ChrisBall/PianoLuce/Arduino/Piano2Midi_Master_Reader/buttonUpdate.ino

void buttonUpdate() {
  for (int i = 0; i < 3; i++) {
    boolean buttonState = digitalRead(buttonPins[i]);
    if (buttonStates[i] == 3) {
      buttonStates[i] = 2;
    }
    if ((buttonState == LOW) && (buttonStates[i] == 0)) {
      buttonStates[i] = 3;
    }
    if (buttonStates[i] == 1) {
      buttonStates[i] = 0;
    }
    if ((buttonState == HIGH) && (buttonStates[i] == 2)) {
      buttonStates[i] = 1;
    }
  }
  //0-off
  //3-momentary on
  //2-on
  //1-momentary off
}
